pa-pa/HMSensor/AddOns/1AAAHolder/files/1AAAHolder.png

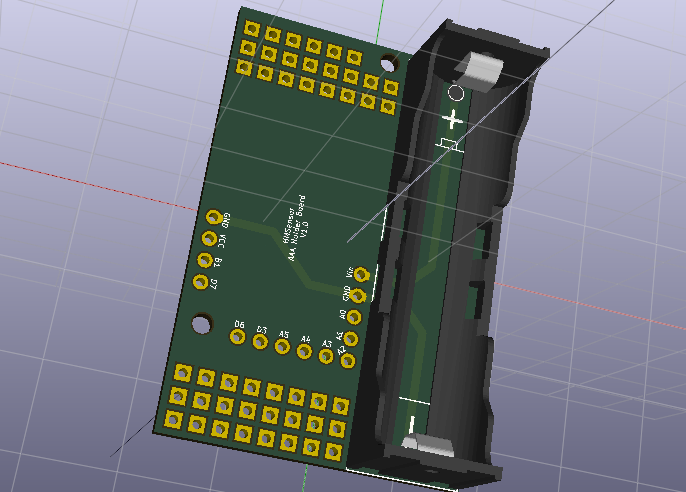
AddOns/1AAAHolder/files/1AAAHolder.png
