pa-pa/HMSensor/AddOns/2AAAHolder/files/2AAAHolder.png

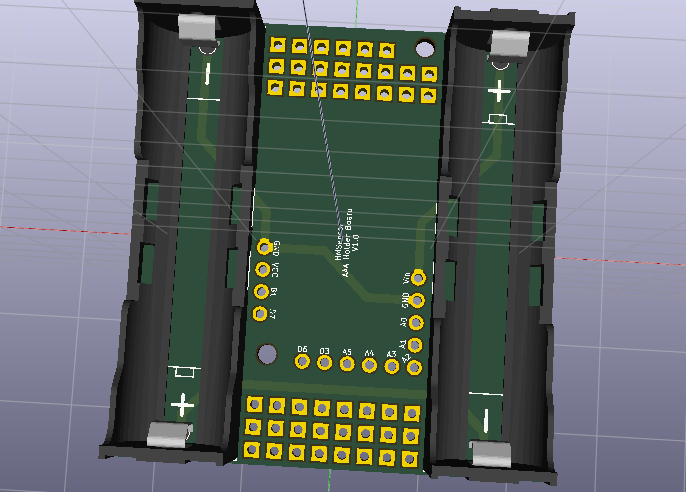
AddOns/2AAAHolder/files/2AAAHolder.png
