pa-pa/HMSensor/AddOns/18650Holder/files/18650Holder.png

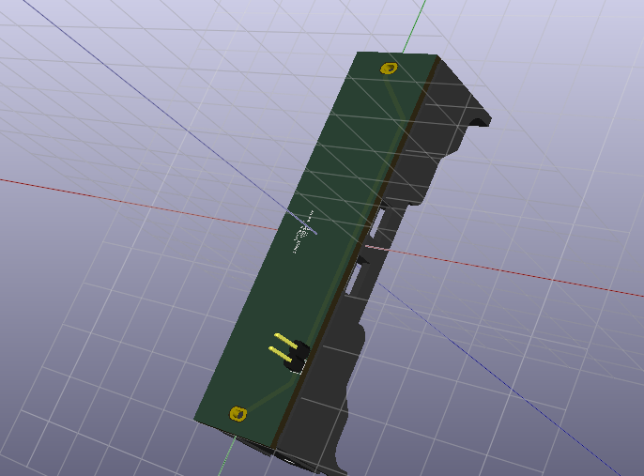
AddOns/18650Holder/files/18650Holder.png
