pa-pa/HMSensor/AddOns/I2CBoard/files/I2CBoard.png

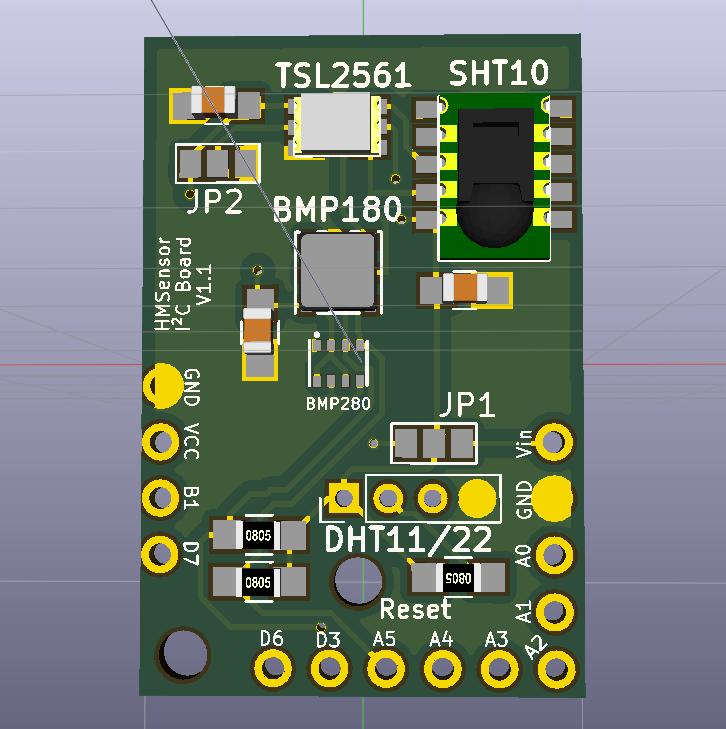
AddOns/I2CBoard/files/I2CBoard.png
