pa-pa/HMSensor/AddOns/PrototypeBoard/files/PrototypeBoard.png

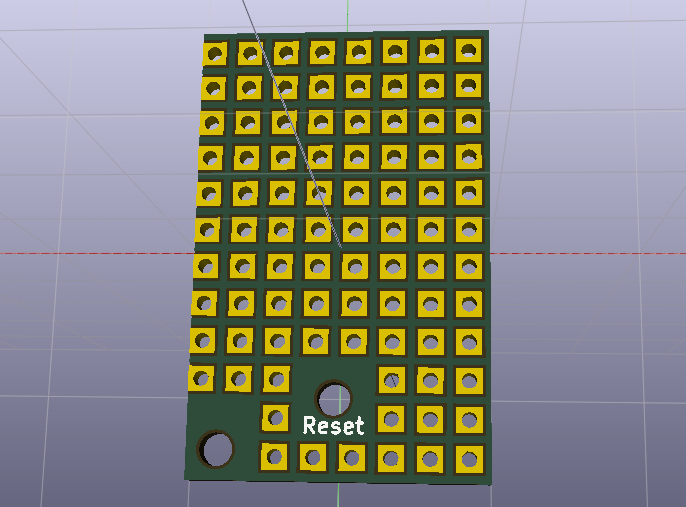
AddOns/PrototypeBoard/files/PrototypeBoard.png
