pa-pa/HMSensor/AddOns/RelayBoard/files/RelayBoard-Front.png

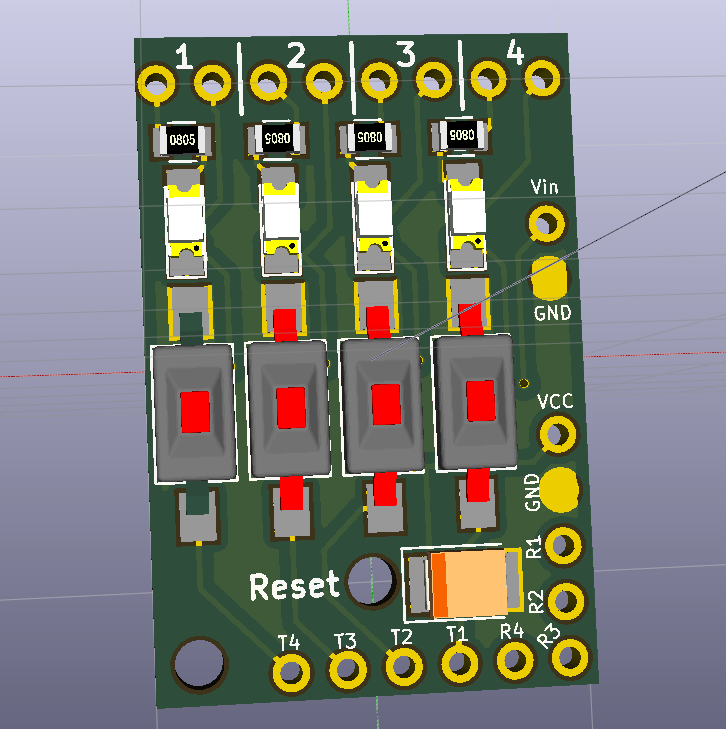
AddOns/RelayBoard/files/RelayBoard-Front.png
