pa-pa/HMSensor/HMSensor-CR2032/files/Back.png

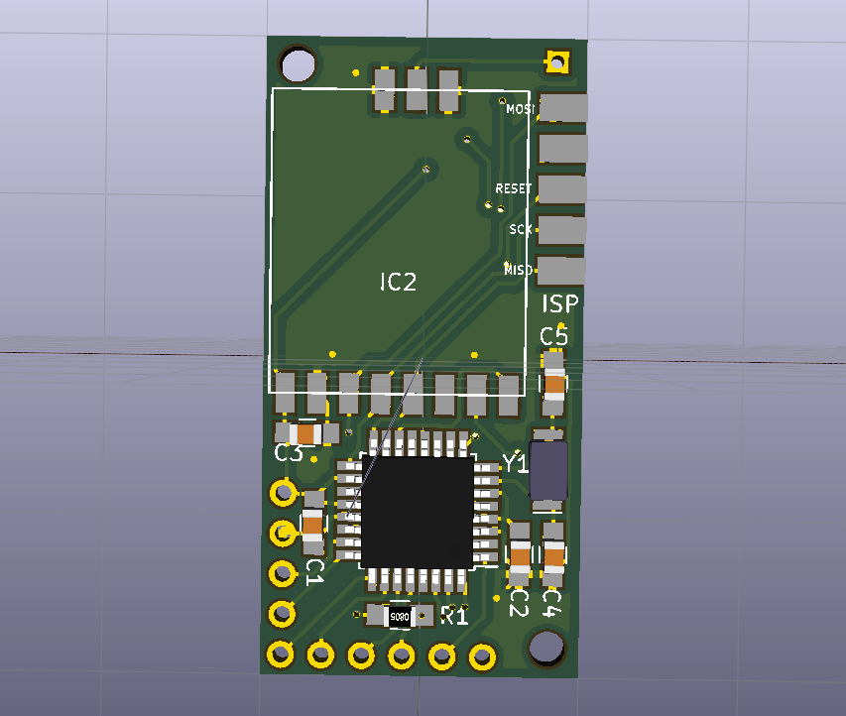
HMSensor-CR2032/files/Back.png
