pa-pa/HMSensor/HMSensor-CR2032/files/Front.png

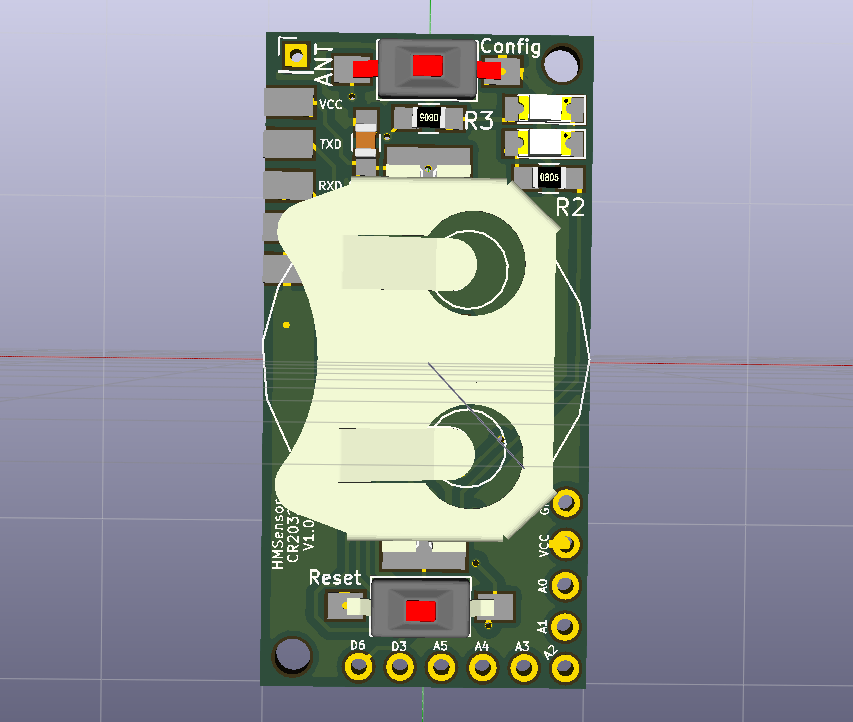
HMSensor-CR2032/files/Front.png
