pa-pa/HMSensor/Panel2/P2_Combined_Bottom.png

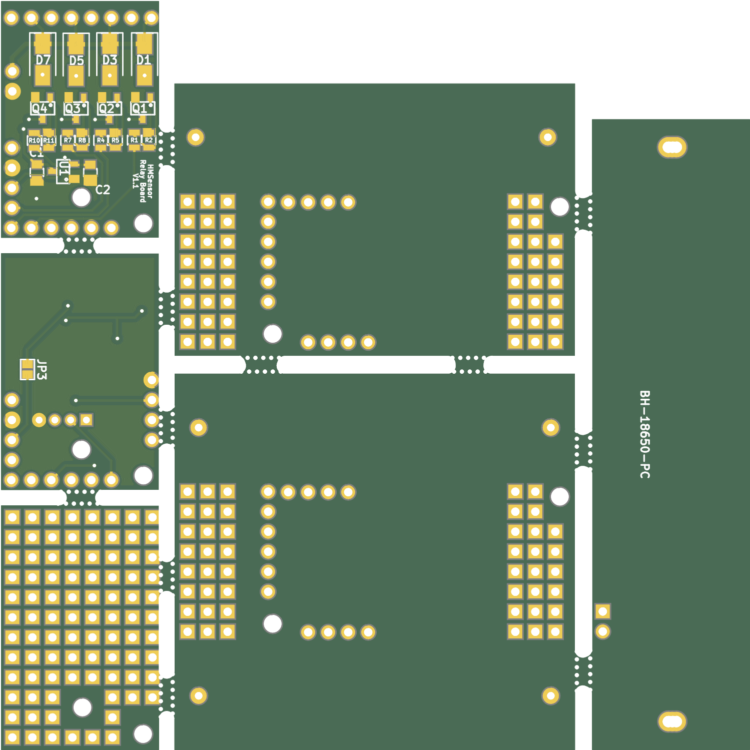
Panel2/P2_Combined_Bottom.png
