pa-pa/HMSensor/Panel2/P2_Combined_Top.png

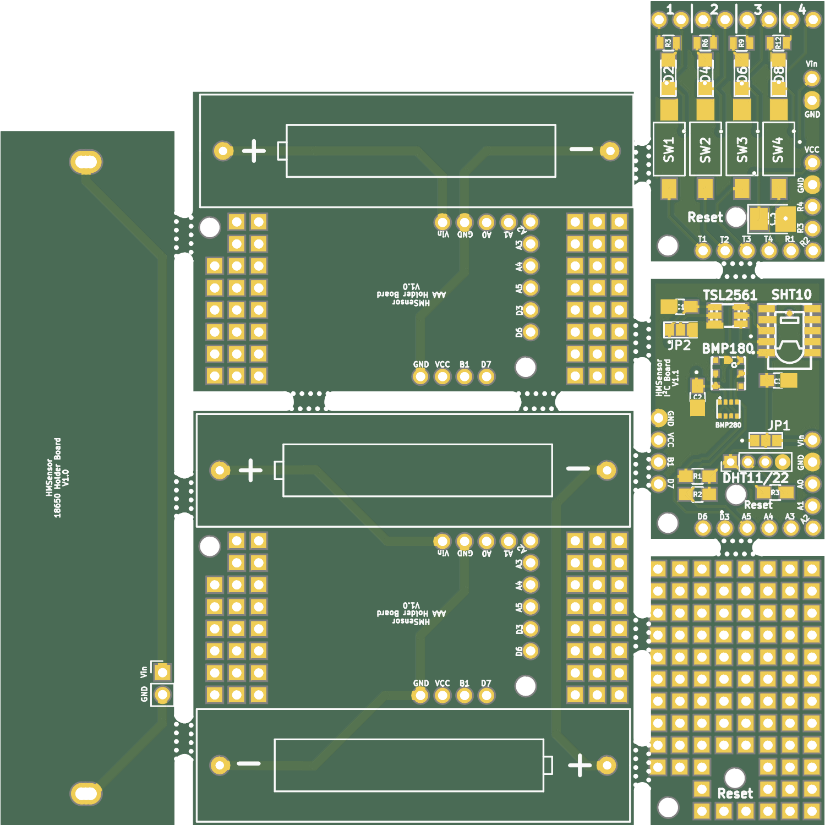
Panel2/P2_Combined_Top.png
