pa-pa/HMSensor/Panel/P1_Combined_Bottom.png

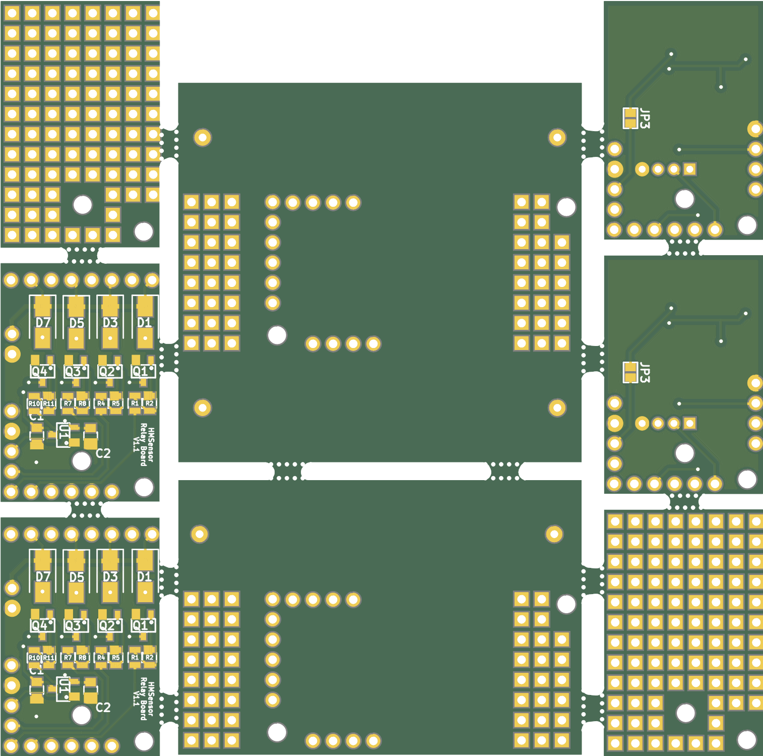
Panel/P1_Combined_Bottom.png
