pa-pa/HMSensor/HMSensor-StepUp/files/Back.png

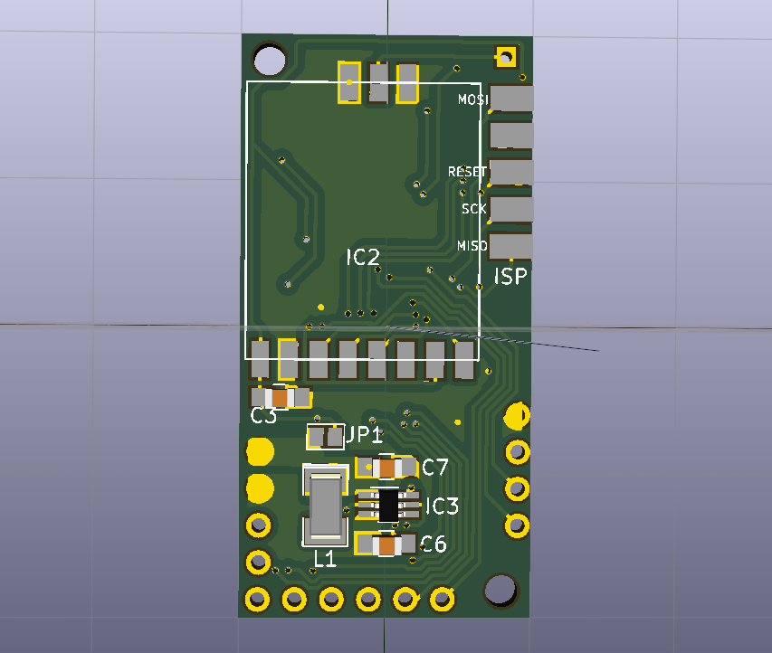
HMSensor-StepUp/files/Back.png
